abidanBrito/murbin/src/embedded/rpi3/rpi_controller/app/src/main/java/com/example/rpi_controller/MainActivity.java

package com.example.rpi_controller;

import android.os.Bundle;

import androidx.appcompat.app.AppCompatActivity;

/**
 * Skeleton of an Android Things activity.
 * <p>
 * Android Things peripheral APIs are accessible through the PeripheralManager
 * For example, the snippet below will open a GPIO pin and set it to HIGH:
 * <p>
 * PeripheralManager manager = PeripheralManager.getInstance();
 * try {
 * Gpio gpio = manager.openGpio("BCM6");
 * gpio.setDirection(Gpio.DIRECTION_OUT_INITIALLY_LOW);
 * gpio.setValue(true);
 * } catch (IOException e) {
 * Log.e(TAG, "Unable to access GPIO");
 * }
 * <p>
 * You can find additional examples on GitHub: https://github.com/androidthings
 */

public class MainActivity extends AppCompatActivity {

    @Override
    protected void onCreate(Bundle savedInstanceState) {
        super.onCreate(savedInstanceState);
        setContentView(R.layout.activity_main);
    }

}
