abidanBrito/murbin/src/mobile_app/Murbin/app/src/main/java/com/example/murbin/presentation/zone/administrator/AdministratorTechnicianEditActivity.java

/*
 * Created by Francisco Javier Paños Madrona on 6/12/20 12:17
 * Copyright (c) 2020 . All rights reserved.
 * Last modified 6/12/20 12:17
 */

package com.example.murbin.presentation.zone.administrator;

import android.annotation.SuppressLint;
import android.app.AlertDialog;
import android.content.Intent;
import android.os.Bundle;
import android.view.Menu;
import android.view.MenuItem;
import android.view.View;
import android.view.ViewGroup;
import android.widget.Button;
import android.widget.EditText;
import android.widget.Spinner;

import androidx.annotation.NonNull;
import androidx.appcompat.widget.Toolbar;

import com.example.murbin.App;
import com.example.murbin.BaseActivity;
import com.example.murbin.R;
import com.example.murbin.data.UsersDatabaseCrud;
import com.example.murbin.models.User;
import com.example.murbin.presentation.zone.administrator.fragments.AdministratorSubzoneSelectActivity;
import com.google.android.material.bottomnavigation.BottomNavigationView;

import java.util.ArrayList;
import java.util.Date;
import java.util.List;

public class AdministratorTechnicianEditActivity extends BaseActivity implements View.OnClickListener {

    private ViewGroup mContainer;
    private Toolbar mToolbar;
    private BottomNavigationView mBottomNavigationView;
    private String m_name;
    private String m_surname;
    private String m_email;
    private String mMessage;
    private String mId;
    private EditText m_et_name, m_et_email, m_et_pass;
    private Button m_btn_cancel, m_btn_save, m_btn_spinner;
    private Spinner m_spinner_subzone;
    private UsersDatabaseCrud mUsersDatabaseCrud;
    private User mUser;
    private List<String> listSubzones;

    @Override
    protected void onCreate(Bundle savedInstanceState) {
        super.onCreate(savedInstanceState);
        setContentView(R.layout.administrator_technicians_edit_formulary);
        listSubzones = new ArrayList<>();
        initializeLayoutElements();
    }

    /**
     * Method to start the layout elements
     */
    private void initializeLayoutElements() {
        // Toolbar menu
        mToolbar = findViewById(R.id.administrator_technicians_edit_toolbar);
        setSupportActionBar(mToolbar);
        if (getSupportActionBar() != null) {
            getSupportActionBar().setDisplayHomeAsUpEnabled(true);
            getSupportActionBar().setDisplayShowHomeEnabled(true);
            getSupportActionBar().setHomeAsUpIndicator(R.drawable.ic_back);
            getSupportActionBar().setTitle("");
        }

        mContainer = findViewById(R.id.administrator_technicians_edit_activity_container);

        m_et_name = findViewById(R.id.administrator_technicians_edit_et_name);
        m_et_pass = findViewById(R.id.administrator_technicians_edit_et_pass);
        m_et_email = findViewById(R.id.administrator_technicians_edit_et_email);

        m_btn_cancel = findViewById(R.id.administrator_technicians_edit_btn_cancelar);
        m_btn_save = findViewById(R.id.administrator_technicians_edit_btn_crear);
        // Al hacer click sobre este boton se abre el spinner.
        m_btn_spinner = findViewById(R.id.administrator_technicians_edit_spinner_subzones);

        m_btn_cancel.setOnClickListener(this);
        m_btn_save.setOnClickListener(this);
        m_btn_spinner.setOnClickListener(this);

        // BottomNavigationView menu
        mBottomNavigationView = findViewById(R.id.administrator_main_activity_bottom_navigation);
        if (App.getInstance().getCurrentUser() != null && App.getInstance().getCurrentUser().getRole().equals(App.ROLE_ROOT)) {
            mBottomNavigationView.getMenu().clear();
            mBottomNavigationView.inflateMenu(R.menu.root_main_bottom_navigation);
            mBottomNavigationView.setSelectedItemId(R.id.root_main_bottom_navigation_technician);
        } else {
            mBottomNavigationView.setSelectedItemId(R.id.administrator_main_bottom_navigation_technician);
        }
        actionsBottomNavigationView();

        Bundle extras = getIntent().getExtras();
        if (extras != null) {
            if (extras.containsKey("message")) {
                mMessage = extras.getString("message", "");
                if (mMessage != null && !mMessage.isEmpty()) {
                    App.getInstance().snackMessage(mContainer, R.color.black, mMessage, this);
                }
            }
            if (extras.containsKey("id")) {
                mId = extras.getString("id", "");

            }
        }

        mUsersDatabaseCrud = new UsersDatabaseCrud();
        mUsersDatabaseCrud.read(mId, user -> {
            mUser = user;
            m_et_name.setText(user.getName());
            m_et_email.setText(user.getEmail());
        });
    }

    @Override
    public boolean onCreateOptionsMenu(Menu menu) {
        getMenuInflater().inflate(R.menu.administrator_technicians_edit_menu, menu);

        return super.onCreateOptionsMenu(menu);
    }

    @SuppressLint("NonConstantResourceId")
    @Override
    public boolean onOptionsItemSelected(MenuItem item) {
        if (item.getItemId() == R.id.administrator_technicians_edit_menu_delete) {
            AlertDialog alertDialog = confirmDeleteDialog();
            alertDialog.show();
        }

        return super.onOptionsItemSelected(item);
    }

    /**
     * Method for bottom navigation functionality
     */
    public void actionsBottomNavigationView() {
        // Actions when pressing an option in the lower navigation
        mBottomNavigationView.setOnNavigationItemSelectedListener(new BottomNavigationView.OnNavigationItemSelectedListener() {
            @SuppressLint("NonConstantResourceId")
            @Override
            public boolean onNavigationItemSelected(@NonNull MenuItem item) {
                Intent intent;
                int id = item.getItemId();
                if (id == R.id.administrator_main_bottom_navigation_home
                        || id == R.id.root_main_bottom_navigation_home) {
                    intent = new Intent(AdministratorTechnicianEditActivity.this, AdministratorMainActivity.class);
                    intent.addFlags(Intent.FLAG_ACTIVITY_CLEAR_TOP | Intent.FLAG_ACTIVITY_NEW_TASK);
                    startActivity(intent);
                } else if (id == R.id.administrator_main_bottom_navigation_subzones
                        || id == R.id.root_main_bottom_navigation_subzones) {
                    intent = new Intent(AdministratorTechnicianEditActivity.this, AdministratorSubzoneListActivity.class);
                    intent.addFlags(Intent.FLAG_ACTIVITY_CLEAR_TOP | Intent.FLAG_ACTIVITY_NEW_TASK);
                    startActivity(intent);
                } else if (id == R.id.administrator_main_bottom_navigation_technician
                        || id == R.id.root_main_bottom_navigation_technician) {
                    // Empty activity
                } else if (id == R.id.root_main_bottom_navigation_administrator) {
                    intent = new Intent(AdministratorTechnicianEditActivity.this, RootAdministratorListActivity.class);
                    intent.addFlags(Intent.FLAG_ACTIVITY_CLEAR_TOP | Intent.FLAG_ACTIVITY_NEW_TASK);
                    startActivity(intent);
                }

                return true;
            }
        });

        // Actions when pressing an option already selected from the lower navigation
        mBottomNavigationView.setOnNavigationItemReselectedListener(new BottomNavigationView.OnNavigationItemReselectedListener() {
            @SuppressLint("NonConstantResourceId")
            @Override
            public void onNavigationItemReselected(@NonNull MenuItem item) {
                int id = item.getItemId();
                if (id == R.id.administrator_main_bottom_navigation_home
                        || id == R.id.root_main_bottom_navigation_home) {
                    // Empty activity
                } else if (id == R.id.administrator_main_bottom_navigation_subzones
                        || id == R.id.root_main_bottom_navigation_subzones) {
                    // Empty action
                } else if (id == R.id.administrator_main_bottom_navigation_technician
                        || id == R.id.root_main_bottom_navigation_technician) {
                    // Empty action
                } else if (id == R.id.root_main_bottom_navigation_administrator) {
                    // Empty action
                }
            }
        });
    }

    @SuppressLint("NonConstantResourceId")
    @Override
    public void onClick(View v) {
        int id = v.getId();
        switch (id) {
            case R.id.administrator_technicians_edit_btn_cancelar: {
                Intent intent = new Intent(AdministratorTechnicianEditActivity.this, AdministratorTechnicianListActivity.class);
                intent.addFlags(Intent.FLAG_ACTIVITY_CLEAR_TOP | Intent.FLAG_ACTIVITY_NEW_TASK);
                intent.putExtra("message", "Acción cancelada.");
                startActivity(intent);

                break;
            }
            case R.id.administrator_technicians_edit_btn_crear: {
                if (checkForm()) {
                    String name = m_et_name.getText().toString();
                    String email = m_et_email.getText().toString();
                    String pass = m_et_pass.getText().toString();
                    User updatedUser = mUser;
                    updatedUser.setName(name);
                    updatedUser.setEmail(email);
                    updatedUser.setListSubzones(listSubzones);
                    if(pass != null && !pass.isEmpty()){
                        updatedUser.setPassword(pass);
                    }
                    updatedUser.setLastAccess(new Date(System.currentTimeMillis()));
                    mUsersDatabaseCrud.update(mId, updatedUser.parseToMap(), response -> {
                        if (response) {
                            Intent intent = new Intent(AdministratorTechnicianEditActivity.this, AdministratorTechnicianListActivity.class);
                            intent.addFlags(Intent.FLAG_ACTIVITY_CLEAR_TOP | Intent.FLAG_ACTIVITY_NEW_TASK);
                            intent.putExtra("message", "Técnico actualizado correctamente.");
                            startActivity(intent);
                        } else {
                            App.getInstance().snackMessage(
                                    mContainer,
                                    R.color.black,
                                    "Error desconocido al actualizar el técnico.",
                                    AdministratorTechnicianEditActivity.this
                            );
                        }
                    });
                    // Update variable with changes
                    mUser = updatedUser;
                }

                break;
            }
            case R.id.administrator_technicians_edit_spinner_subzones: {
//                // Set subzone spinner entries
//                String[] subzoneArray = {"Grau", "Platja"}; // Array with the all the subzones
//                ArrayAdapter<String> spinnerArrayAdapter = new ArrayAdapter<String>(this, android.R.layout.simple_spinner_item, subzoneArray );
//                m_spinner_subzone.setAdapter(spinnerArrayAdapter);
//                m_spinner_subzone.setVisibility(View.VISIBLE);
//                m_spinner_subzone.performClick();
                Intent intent = new Intent(AdministratorTechnicianEditActivity.this, AdministratorSubzoneSelectActivity.class);
                startActivity(intent);

                break;
            }
        }
    }

    /**
     * @return AlertDialog
     */
    private AlertDialog confirmDeleteDialog() {
        return new AlertDialog.Builder(this)
                .setTitle(getString(R.string.AdministratorTechnicianEditActivity_alert_dialog_delete_title))
                .setMessage(getString(R.string.AdministratorTechnicianEditActivity_alert_dialog_delete_message))
                .setIcon(android.R.drawable.stat_sys_warning)
                .setPositiveButton(getString(R.string.AdministratorTechnicianEditActivity_alert_dialog_confirm_text), (dialog, whichButton) -> {
                    mUsersDatabaseCrud.delete(mId, response -> {
                        Intent intent = new Intent(AdministratorTechnicianEditActivity.this, AdministratorTechnicianListActivity.class);
                        intent.addFlags(Intent.FLAG_ACTIVITY_CLEAR_TOP | Intent.FLAG_ACTIVITY_NEW_TASK);
                        if (response) {
                            intent.putExtra("message", "Técnico eliminado correctamente.");
                        } else {
                            intent.putExtra("message", "Error desconocido al eliminar el técnico.");
                        }
                        startActivity(intent);
                        dialog.dismiss();
                    });
                    dialog.dismiss();
                })
                .setNegativeButton(getString(R.string.AdministratorTechnicianEditActivity_alert_dialog_cancel_text), (dialog, which) -> dialog.dismiss())
                .create();
    }

    /**
     * Check if form is correctly
     *
     * @return boolean
     */
    private boolean checkForm() {
        boolean result = true;

        m_name = m_et_name.getText().toString();
        m_email = m_et_email.getText().toString();

        if (m_name.equals("") || m_name.length() < 3) {
            m_et_name.setError("Debes indicar un nombre y de al menos 3 carácteres.");
            result = false;
        }
        if (m_email.equals("") || !App.isValidEmail(m_email)) {
            m_et_email.setError("Debes indicar un m_email válido.");
            result = false;
        }

        return result;
    }

    /**
     *
     * @param listSubzones List<String>
     */
    public void setListSubzones(List<String> listSubzones) {
        this.listSubzones = listSubzones;
        if (!listSubzones.isEmpty()) {
            m_btn_spinner.setHint(R.string.AdministratorSubzoneCreateActivity_alert_dialog_location_message);
        } else {
            m_btn_spinner.setHint(R.string.global_string_location);
        }
    }
}
